Fattoresaimon/I2CEncoderV2.1/Firmware/I2CEncoderV2.1.X/Encoder.h

#ifndef ENCODER_H
#define	ENCODER_H

#include <xc.h> // include processor files - each processor file is guarded.  


#ifdef	__cplusplus
extern "C" {
#endif /* __cplusplus */

extern volatile uint8_t X1_p;
extern volatile uint8_t X1_n;
extern volatile uint8_t X2_p;
extern volatile uint8_t X2_n;
extern volatile uint8_t X4_p;
extern volatile uint8_t X4_pp;
extern volatile uint8_t X4_n;
extern volatile uint8_t X4_nn;
    
#define PB_DEBOUNCE 50

    /** FSM for the push button **/
    typedef enum {
        ENCODER_WAITPUSH,
        ENCODER_WAITRELEASE,
        ENCODER_WAITDOUBLEPUSH,
        ENCODER_WAITDOUBLERELEASED,
        ENCODER_DOUBLEDELAY,       
        ENCODER_TIMEOUT,
        ENCODER_PUSHRESET,
    } ENCODER_SWITCH_STATUS;

    bool EncoderSwitch_GetValue(void);
    bool EncoderSwitch_GetValueFiltered(void);
    void Encoder_AB_Interrupt(void);
    void CLC_1_Interrupt(void);
    void CLC_2_Interrupt(void);

    void FADE_LEDS(void);
    void Encoder_PushButton_FSM(void);
    void Encoder_FSM(void);


#ifdef	__cplusplus
}
#endif /* __cplusplus */

#endif	/* XC_HEADER_TEMPLATE_H */
